McOrts/taller-iot-sensor_radiactividad/img/IMG_2736.jpg

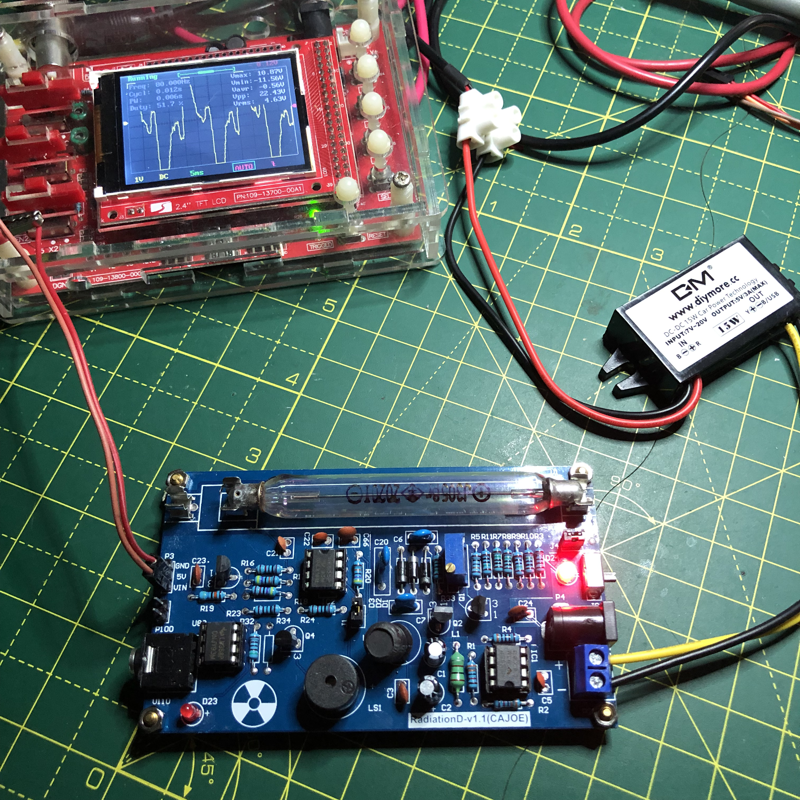
img/IMG_2736.jpg
