McOrts/taller-iot-sensor_radiactividad/img/IMG_2737.jpg

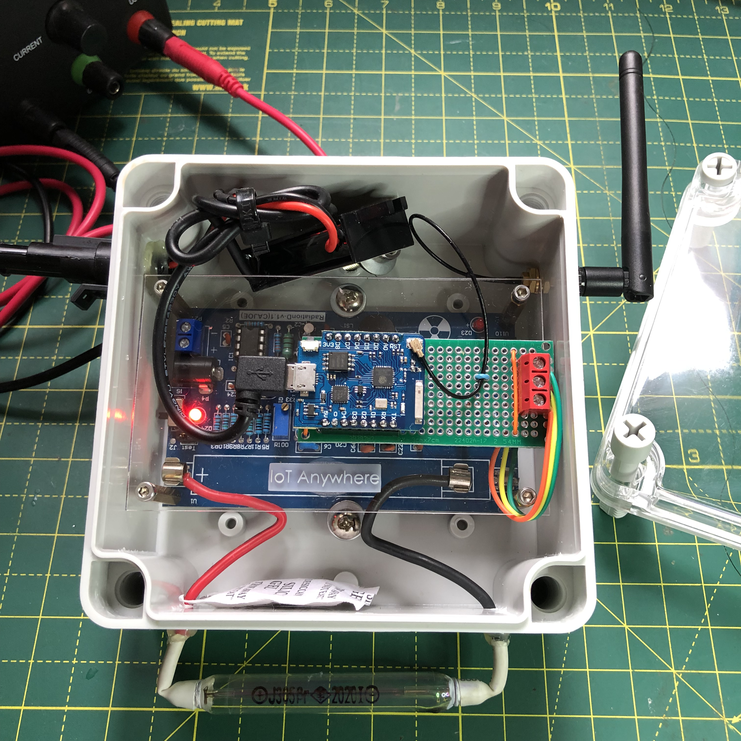
img/IMG_2737.jpg
