McOrts/taller-iot-sensor_radiactividad/img/IMG_2782.jpg

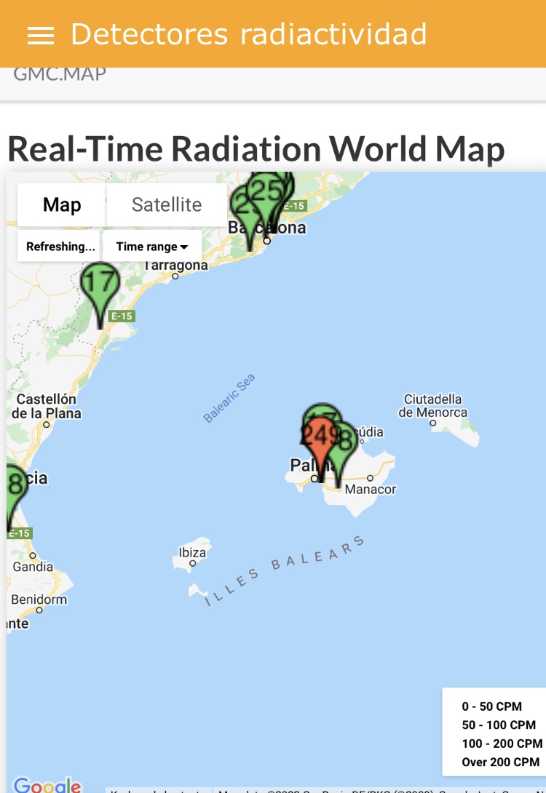
img/IMG_2782.jpg
