McOrts/taller-iot-sensor_radiactividad/img/IoT_nuclear_radiation_sensor_dashboard.png

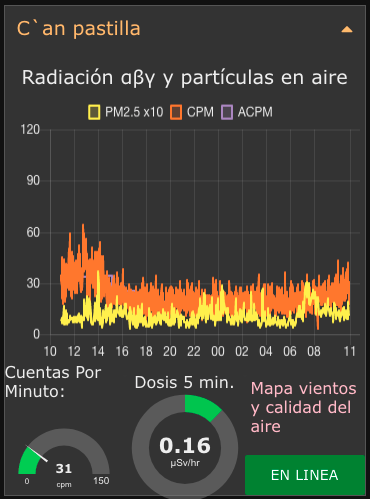
img/IoT_nuclear_radiation_sensor_dashboard.png
