McOrts/taller-iot-sensor_radiactividad/img/map_location.png

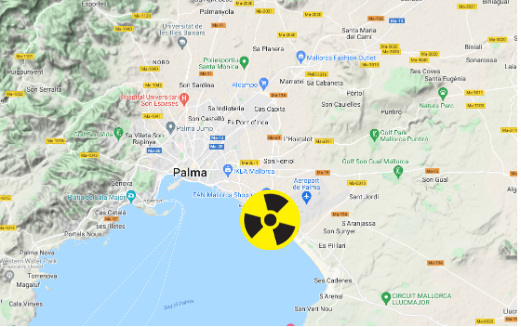
img/map_location.png
